kailashjagadeesh/LineFollower/Gen3/Tracks/trialTrack.pdf

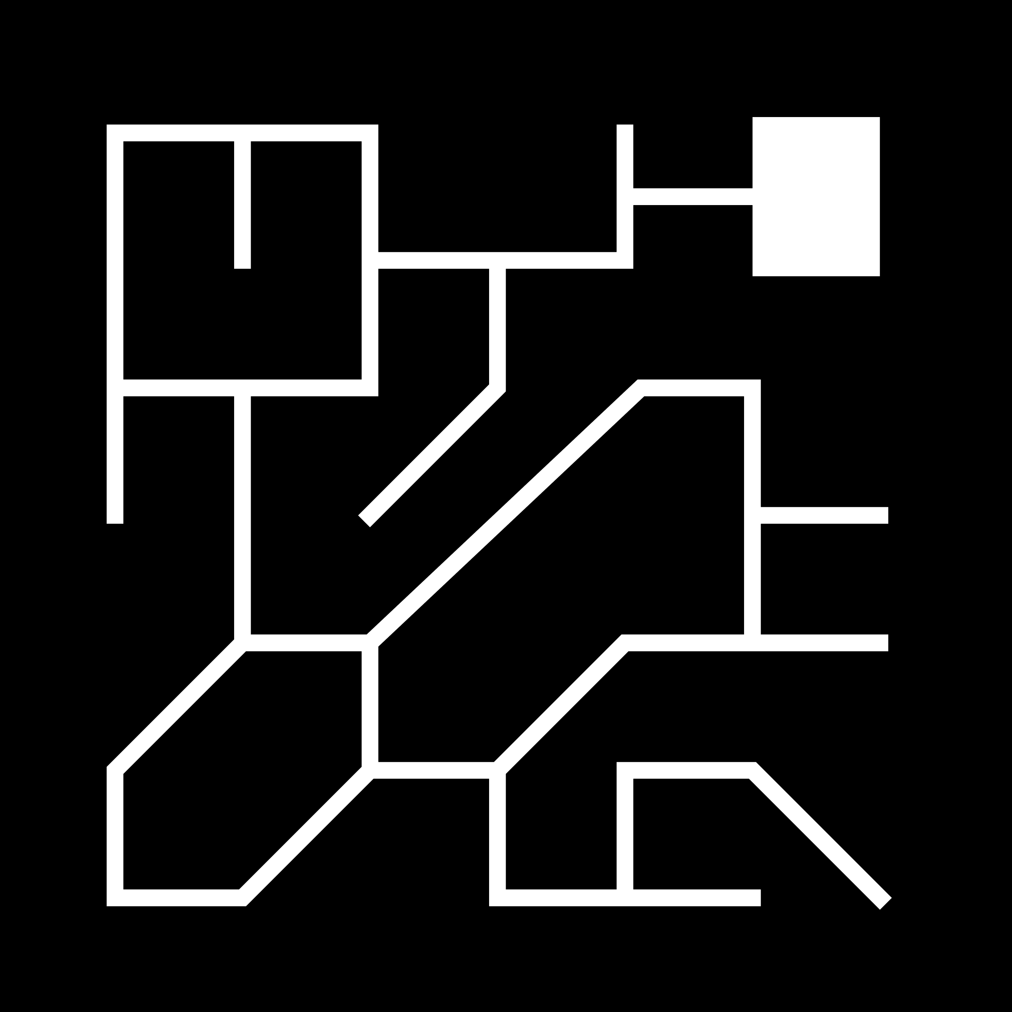
[picture p3: page 1]
