kailashjagadeesh/LineFollower/Gen3/Tracks/trialTrackInverted.pdf

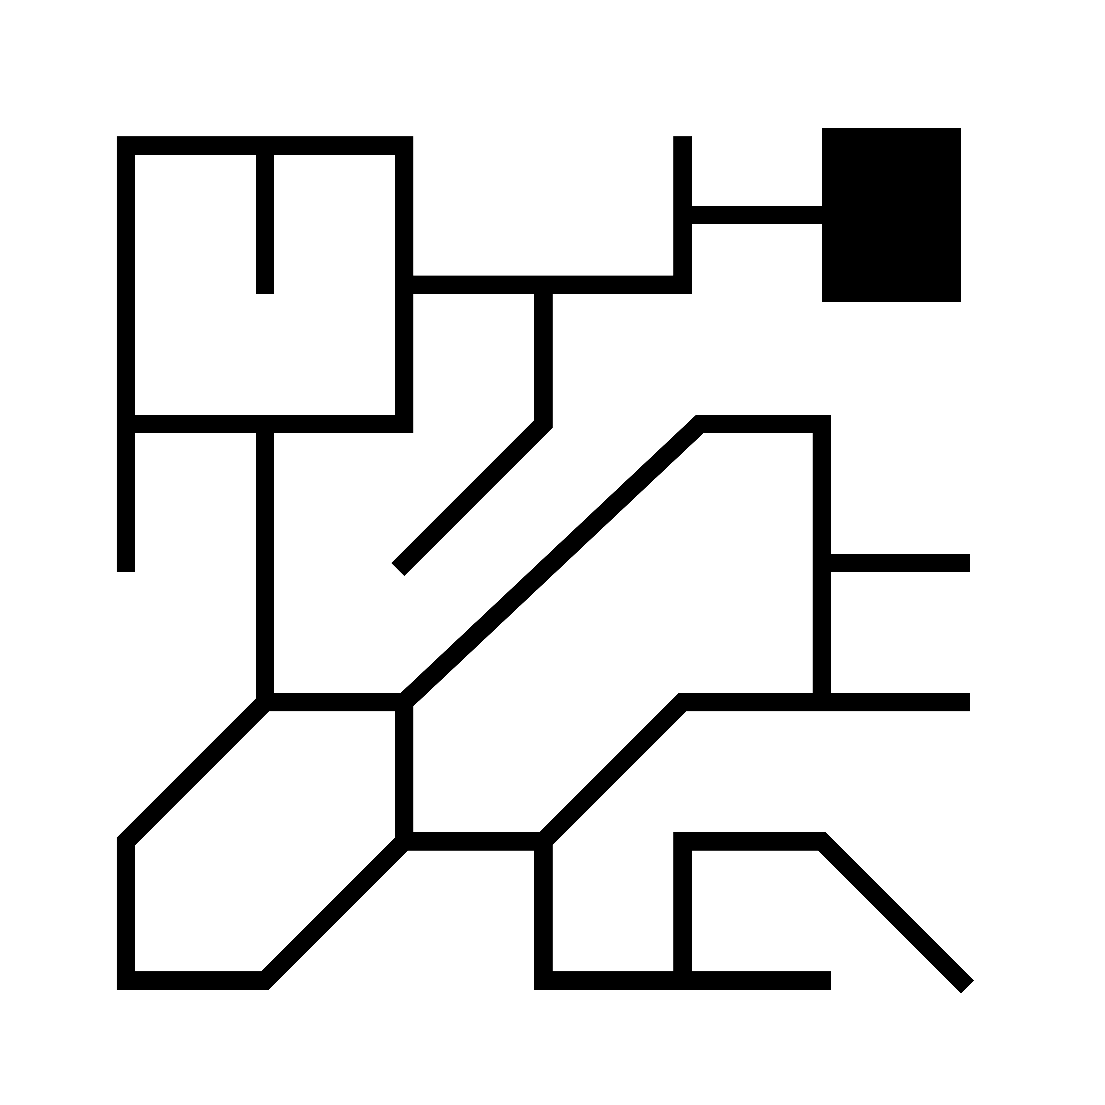
[picture p4: page 1]
