kailashjagadeesh/LineFollower/Gen3/Designs/sensorsPCB/Exports/Etchable PDF/sensors_etch_silk_bottom.pdf

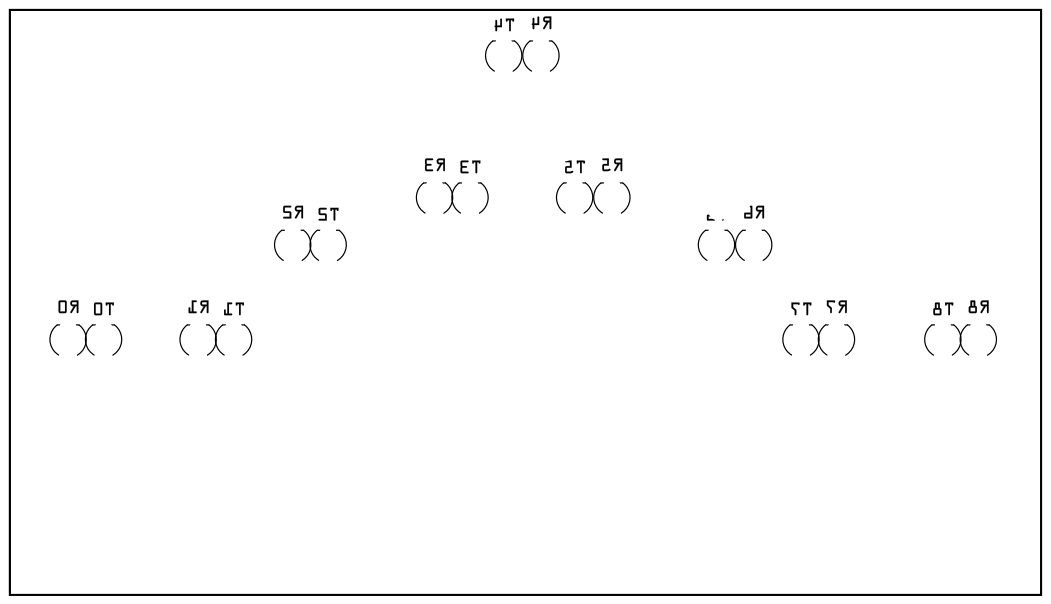
[picture p14: page 1]
