kailashjagadeesh/LineFollower/Gen3/Designs/sensorsPCB/Exports/Etchable PDF/sensors_etch_silk_bottom_mirror.pdf

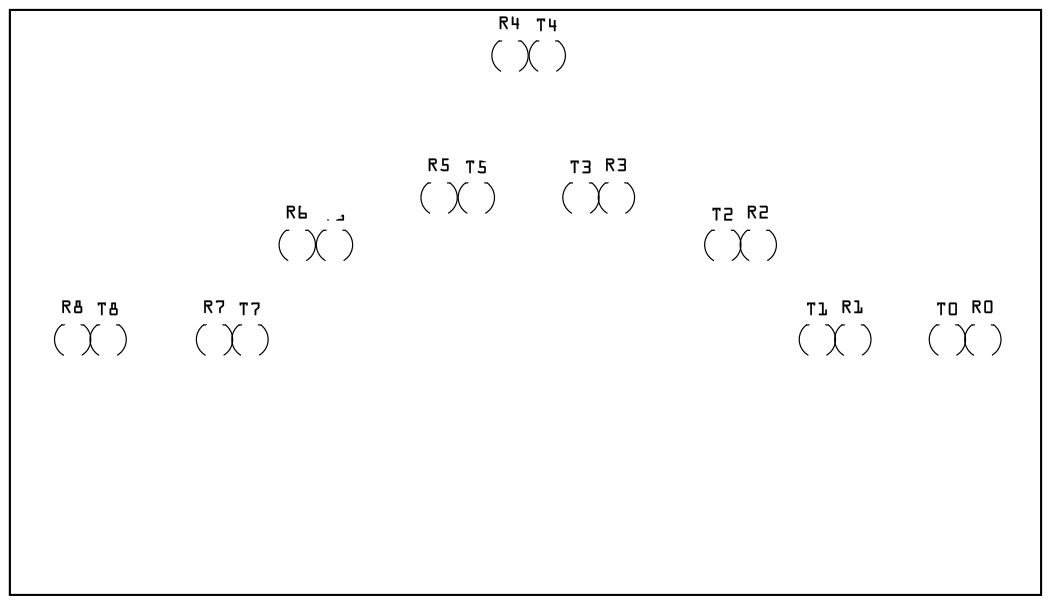
[picture p15: page 1]
