kailashjagadeesh/LineFollower/Gen3/Designs/sensorsPCB/Exports/Etchable PDF/sensors_etch_silk_top.pdf

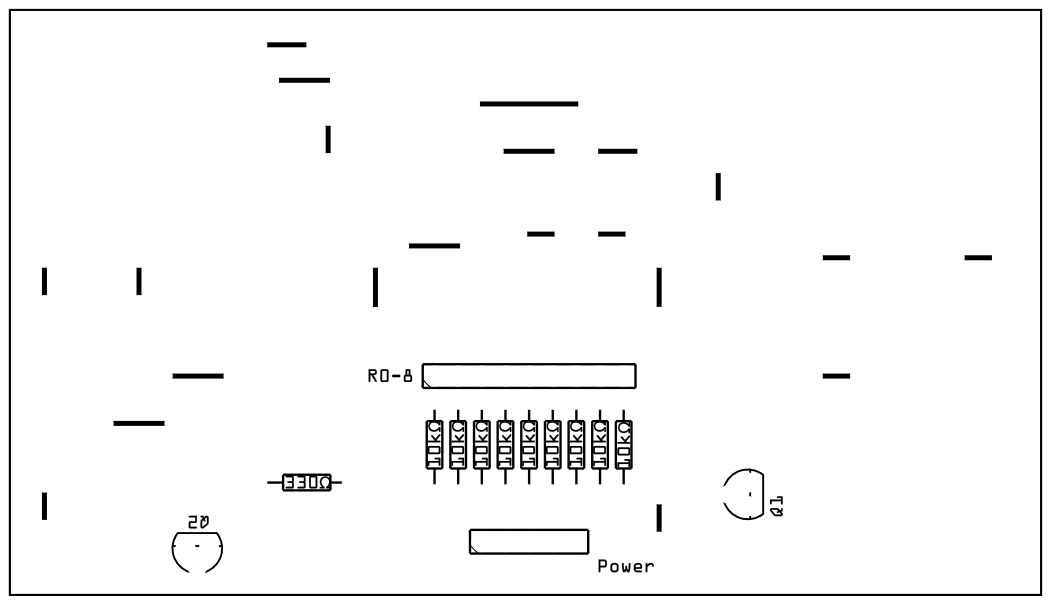
[picture p16: page 1]
