kailashjagadeesh/LineFollower/Gen3/Designs/sensorsPCB/Exports/Etchable PDF/sensors_etch_silk_top_mirror.pdf

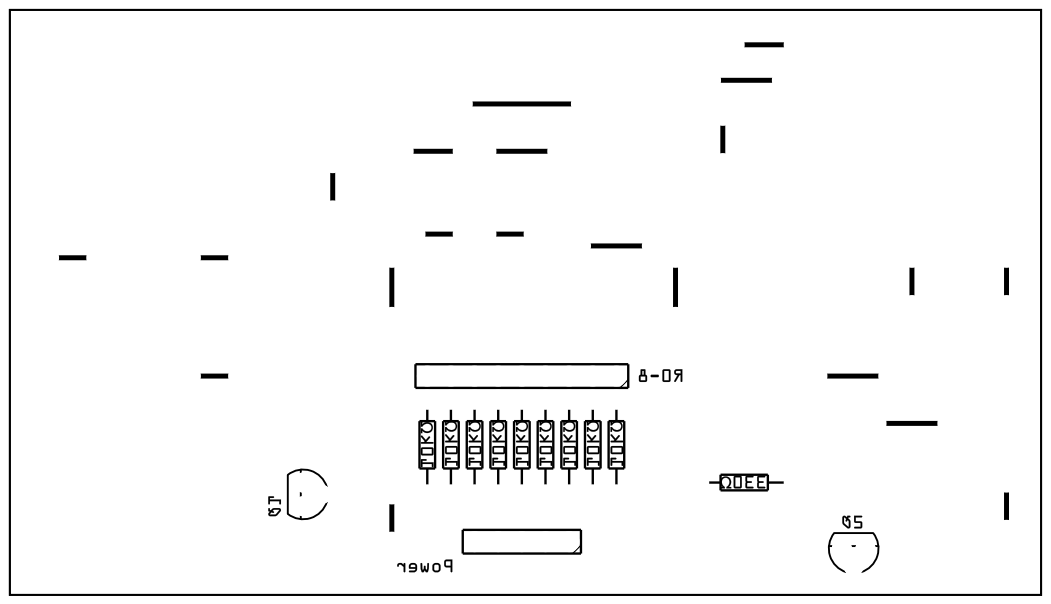
[picture p17: page 1]
