kailashjagadeesh/LineFollower/Gen3/src/LEDInterface/LEDInterface.cpp

#include "LEDInterface.h"
#include "../configure.h"
#include <Arduino.h>

#ifndef NUM_LED
#define NUM_LED 2
#endif

#ifndef LED_PINS
#define LED_PINS {14, 15}
#endif

const int * const LED::pins = new int[NUM_LED] LED_PINS;
const int LED::nPins = NUM_LED;
bool LED::initialized = false;

void LED::init() {
    for (int i = 0; i < nPins; ++i)
        pinMode(pins[i], OUTPUT);

    initialized = true;
}

void LED::toggle(int i) {
    if (!initialized)
        init();
        
    digitalWrite(pins[i], !digitalRead(pins[i]));
}

void LED::write(int i, int v) {
    if (!initialized)
        init();

    digitalWrite(pins[i], v);
}
